alicjamusial/meteo-station-pcb/meteo_station/graphics/background.png

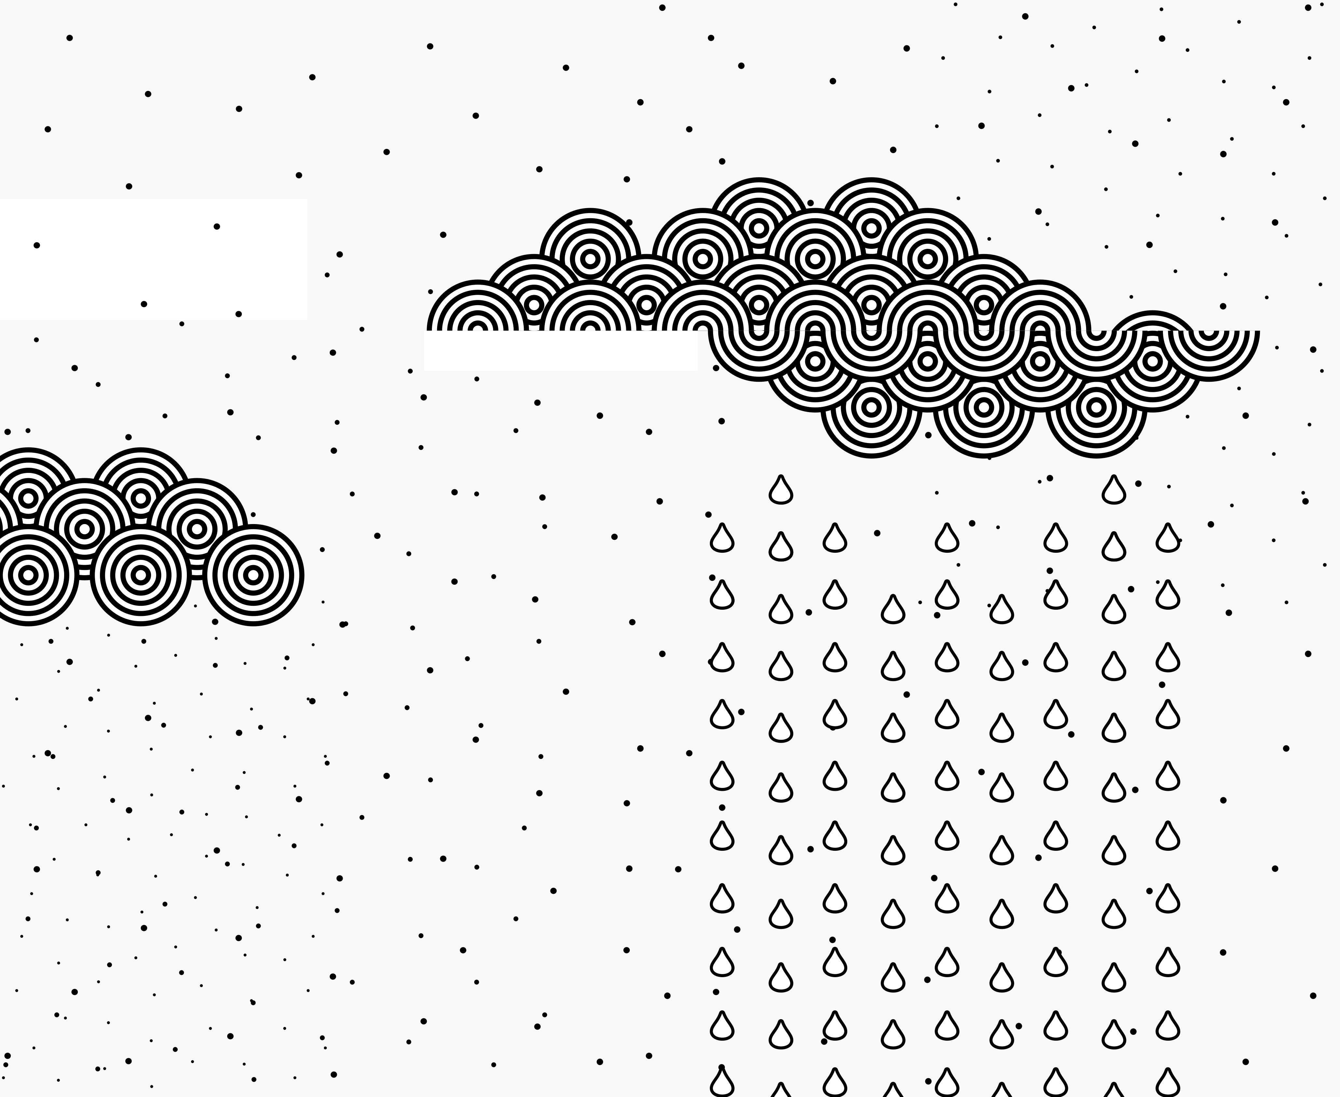
meteo_station/graphics/background.png
