alicjamusial/meteo-station-pcb/meteo_station/graphics/chmurka.png

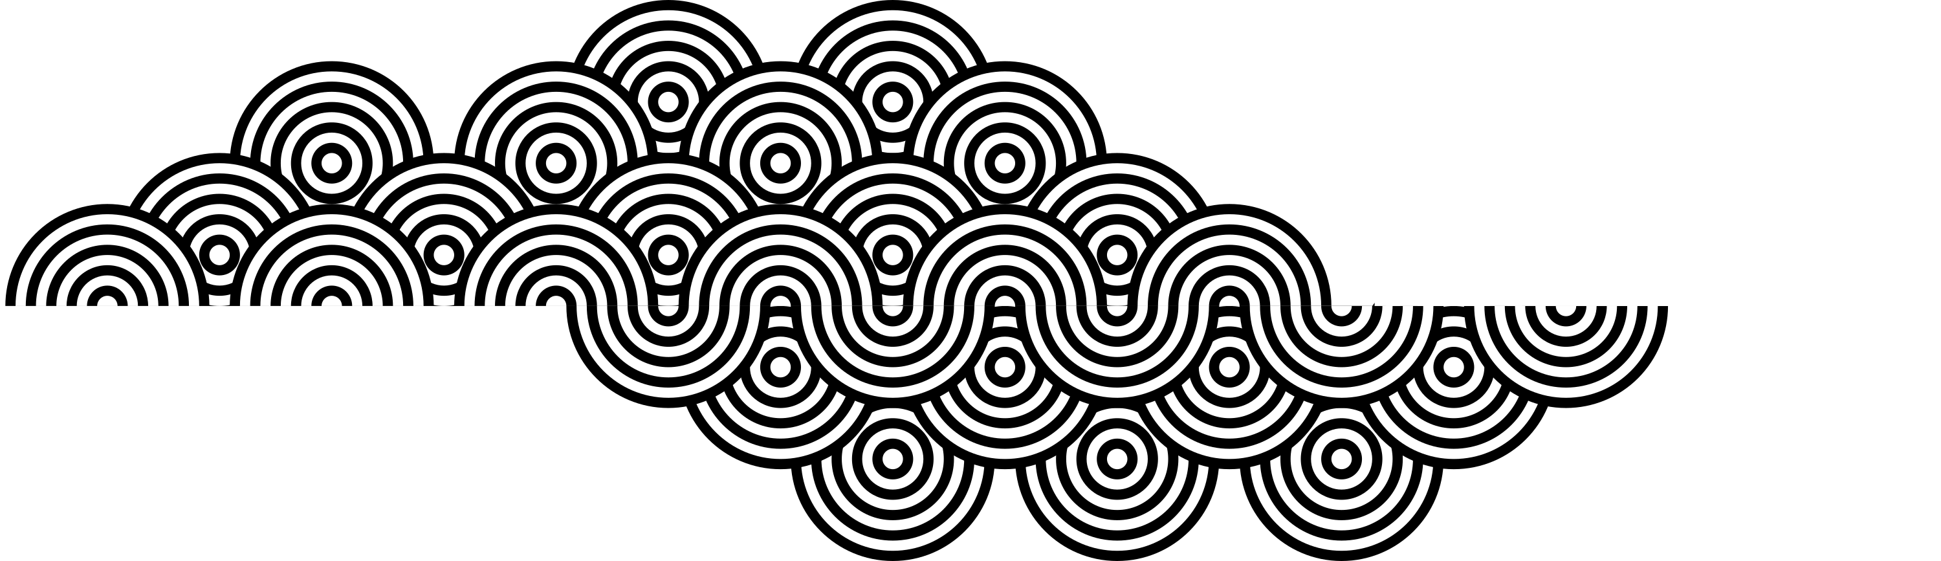
meteo_station/graphics/chmurka.png
