alicjamusial/meteo-station-pcb/meteo_station/graphics/version.png

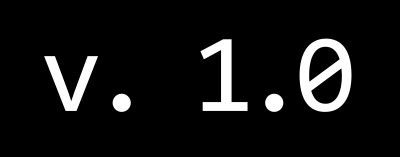
meteo_station/graphics/version.png
